wicked-rainman/ESP32S3_I2C_Cluster/StampS3-Master-node/include/defines.h

#define DEDUPE_SHORT_BUF_SIZE 1000
#define DEDUPE_LONG_BUF_SIZE 5000
#define BEACON_RECORD_SIZE 200
#define UDPBEACON_PORT 5128
#define SSID_MODE_RSSI 2 
#define SSID_MODE_SSID 0
#define SSID_MODE_ASSOC 1
#define LED 21
#define NUM_LEDS 1
#define PIN_BUTTON 0
