wicked-rainman/ESP32S3_I2C_Cluster/StampS3-Network_scan-node/include/defines.h

#define SCAN_INTERVAL 2000
#define ROLL_FIX_DELAY 5000
#define BLUE_LIST_SIZE 8
#define MAX_SSID_STORE_SIZE 200
#define MAX_SSID_LENGTH 35
#define LED 21
#define BUTTON 9
#define NUM_LEDS 1
